mntmn/amiga2000-gfxcard/pics/proto1/oe-patch.jpg

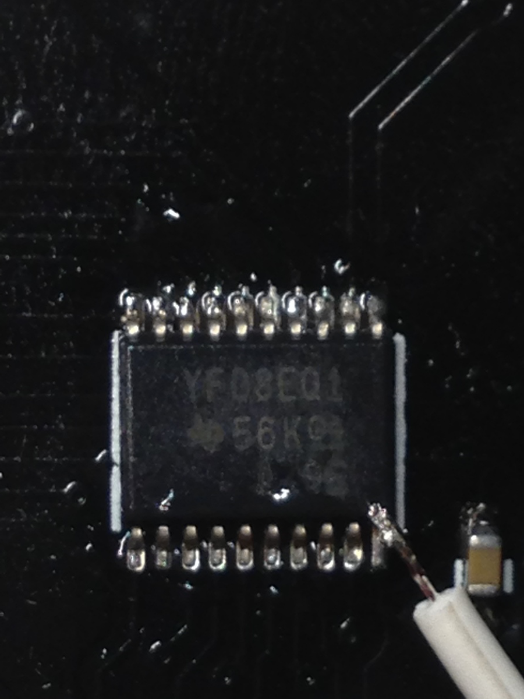
pics/proto1/oe-patch.jpg
