mntmn/amiga2000-gfxcard/pics/proto1/proto1-pcb.png

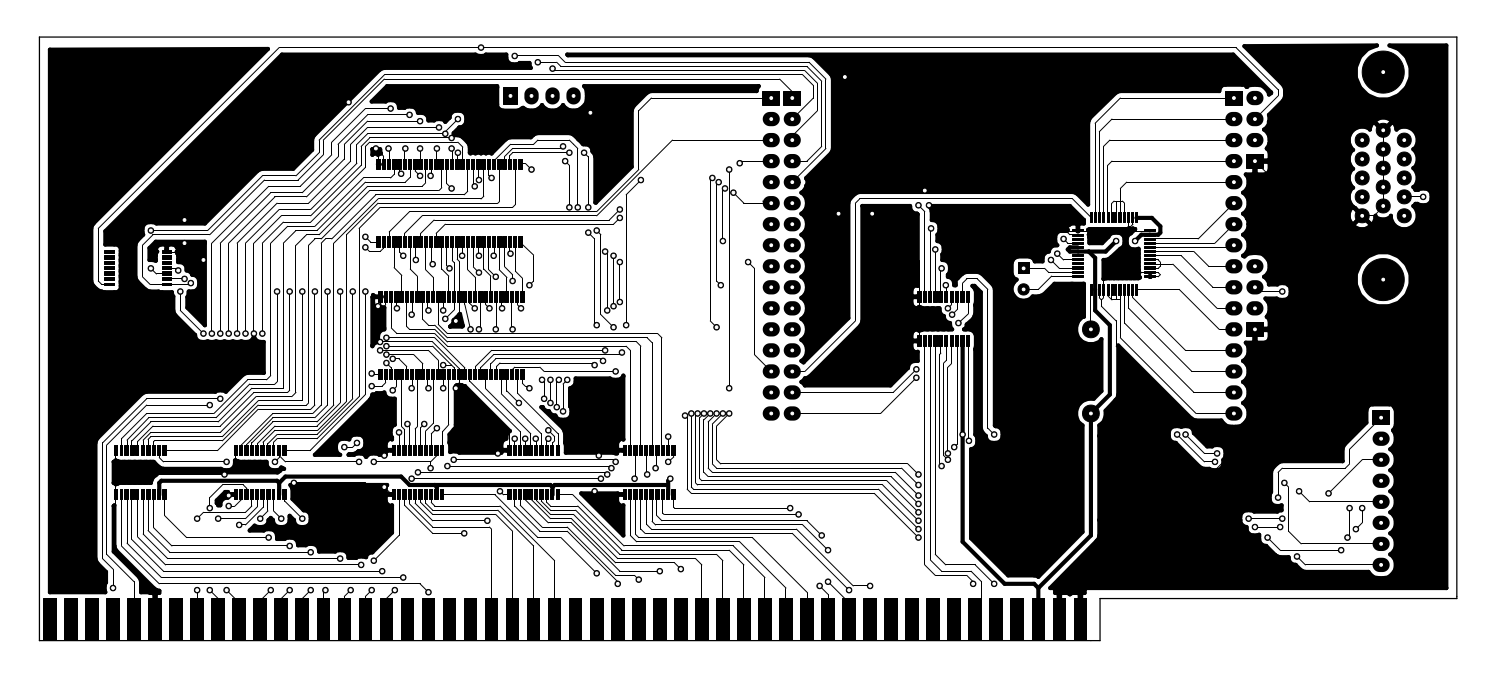
pics/proto1/proto1-pcb.png
