mntmn/amiga2000-gfxcard/pics/proto1/proto1-signals1.jpg

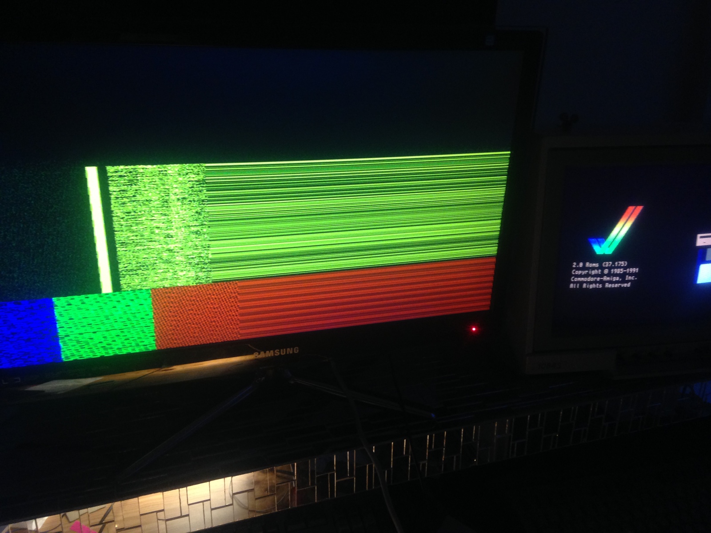
pics/proto1/proto1-signals1.jpg
