mntmn/amiga2000-gfxcard/pics/proto1/zorro-signals1.jpg

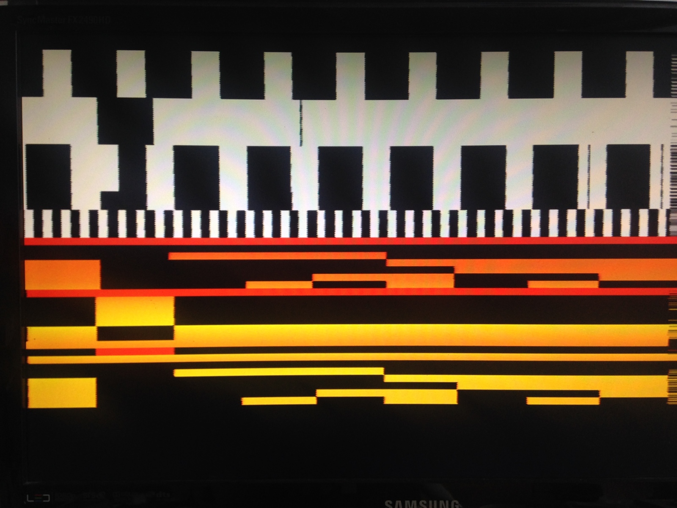
pics/proto1/zorro-signals1.jpg
