mntmn/amiga2000-gfxcard/pics/proto2/proto2-mysticview.jpg

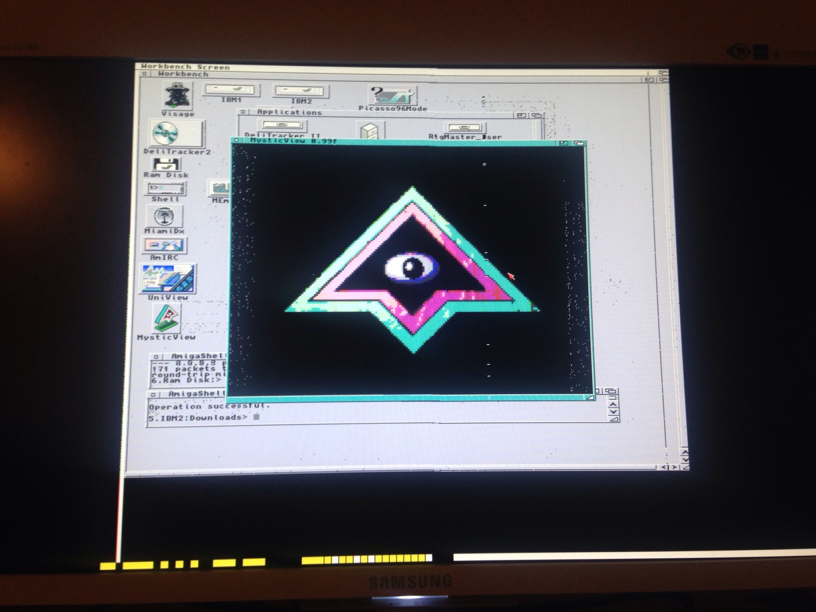
pics/proto2/proto2-mysticview.jpg
