mntmn/amiga2000-gfxcard/pics/proto2/proto2-populated1.jpg

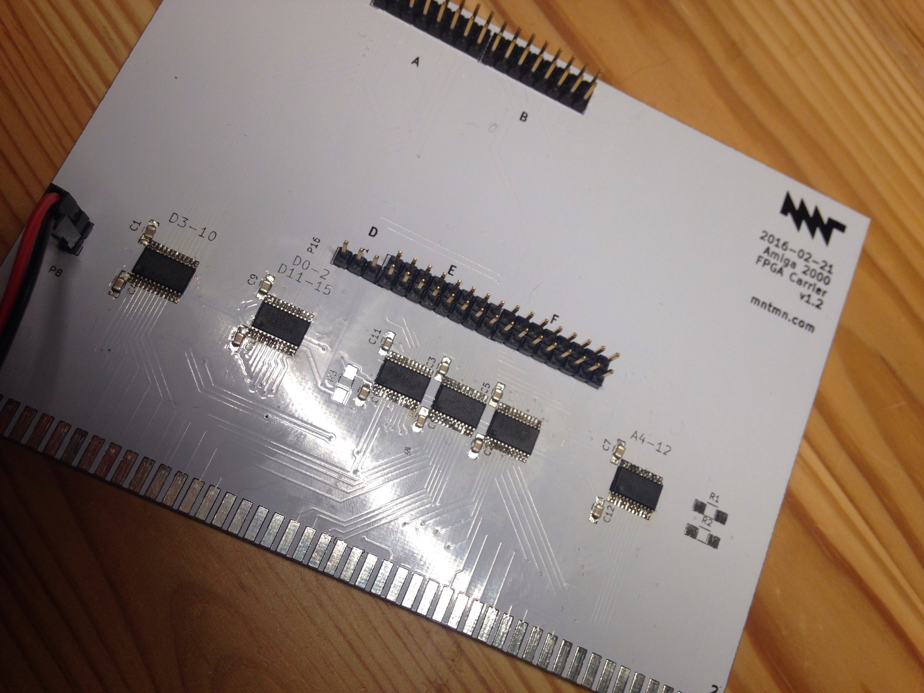
pics/proto2/proto2-populated1.jpg
