mntmn/amiga2000-gfxcard/pics/proto2/proto2-shell.jpg

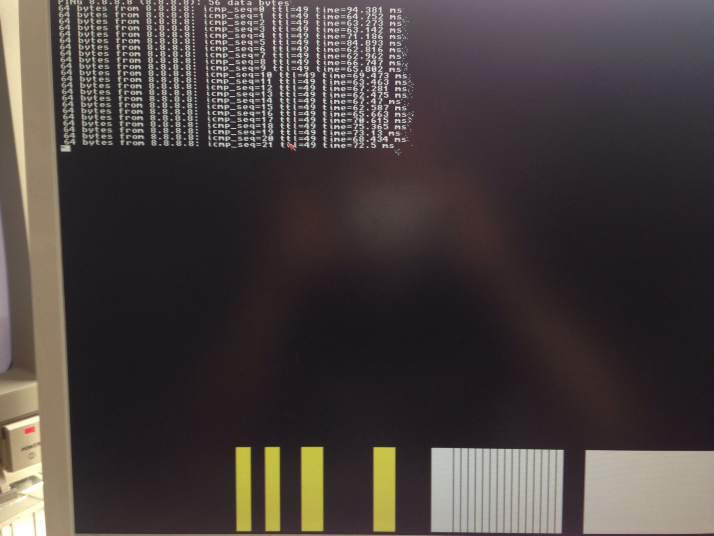
pics/proto2/proto2-shell.jpg
