mntmn/amiga2000-gfxcard/pics/proto2/proto2-signals.jpg

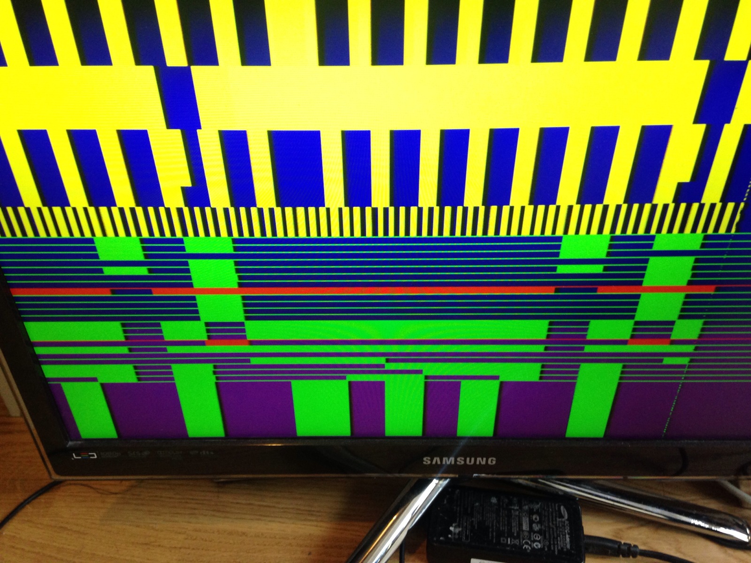
pics/proto2/proto2-signals.jpg
