mntmn/amiga2000-gfxcard/va2000-spartan6/dvid_out.vhd

--------------------------------------------------------------------------------
-- Engineer:      Mike Field <hamster@snap.net.nz>
-- Description:   Converts VGA signals into DVID bitstreams.
--
--                'blank' must be asserted during the non-display 
--                portions of the frame
--
-- NOTE due to the PLL frequency limits, changes are needed in dvid_out_clocking
-- to select pixel rates between 40 and 100 Mhz pixel clocks, or between 20 and 
-- 50 MHz.
--------------------------------------------------------------------------------
library IEEE;
use IEEE.STD_LOGIC_1164.ALL;
Library UNISIM;
use UNISIM.vcomponents.all;

entity dvid_out is
  Port ( -- Clocking
    clk_pixel : IN std_logic;
    -- Pixel data
    red_p     : in  STD_LOGIC_VECTOR (7 downto 0);
    green_p   : in  STD_LOGIC_VECTOR (7 downto 0);
    blue_p    : in  STD_LOGIC_VECTOR (7 downto 0);
    blank     : in  STD_LOGIC;
    hsync     : in  STD_LOGIC;
    vsync     : in  STD_LOGIC;
    reset : in STD_LOGIC;
    -- TMDS outputs
    tmds_out_p : out  STD_LOGIC_VECTOR(3 downto 0);
    tmds_out_n : out  STD_LOGIC_VECTOR(3 downto 0)
  );
end dvid_out;

architecture Behavioral of dvid_out is
  COMPONENT dvid_out_clocking
  PORT(
    clk_pixel : IN std_logic;
    reset : IN std_logic;
    clk_x1 : OUT std_logic;
    clk_x2 : OUT std_logic;
    clk_x10 : OUT std_logic;
    serdes_strobe : OUT std_logic
  );
  END COMPONENT;

  COMPONENT TMDS_encoder
  PORT(
    clk     : IN  std_logic;
    data    : IN  std_logic_vector(7 downto 0);
    c       : IN  std_logic_vector(1 downto 0);
    blank   : IN  std_logic;          
    encoded : OUT std_logic_vector(9 downto 0)
  );
  END COMPONENT;

  COMPONENT tmds_out_fifo
  PORT (
    wr_clk     : IN  STD_LOGIC;
    rd_clk     : IN  STD_LOGIC;
    din        : IN  STD_LOGIC_VECTOR(29 DOWNTO 0);
    wr_en      : IN  STD_LOGIC;
    rd_en      : IN  STD_LOGIC;
    dout       : OUT STD_LOGIC_VECTOR(29 DOWNTO 0);
    full       : OUT STD_LOGIC;
    empty      : OUT STD_LOGIC;
    prog_empty : OUT STD_LOGIC
  );
  END COMPONENT;

  COMPONENT output_serialiser
  PORT(
    clk_load   : IN  std_logic;
    clk_output : IN  std_logic;
    strobe     : IN  std_logic;
    ser_data   : IN  std_logic_vector(4 downto 0);        
    reset   : IN  std_logic;  
    ser_output : OUT std_logic
		);
  END COMPONENT;

  signal clk_x1          : std_logic;
  signal clk_x2          : std_logic;
  signal clk_x10         : std_logic;
  signal serdes_strobe   : std_logic;

  signal encoded_red, encoded_green, encoded_blue : std_logic_vector(9 downto 0);
  signal latched_red, latched_green, latched_blue : std_logic_vector(9 downto 0) := (others => '0');
  signal ser_in_red,  ser_in_green,  ser_in_blue, ser_in_clock   : std_logic_vector(4 downto 0) := (others => '0');
  signal fifo_in       : std_logic_vector(29 downto 0);
  signal fifo_out      : std_logic_vector(29 downto 0);
  signal rd_enable     : std_logic := '0';
  signal not_ready_yet : std_logic;

  signal c_red       : std_logic_vector(1 downto 0); -- := (others => '0');
  signal c_green     : std_logic_vector(1 downto 0); -- := (others => '0');
  signal c_blue      : std_logic_vector(1 downto 0);

  signal red_s     : STD_LOGIC;
  signal green_s   : STD_LOGIC;
  signal blue_s    : STD_LOGIC;
  signal clock_s   : STD_LOGIC;

begin   
  -- Send the pixels to the encoder
  c_blue <= "00"; -- vsync & hsync;
  c_red <= vsync & hsync;
  c_green <= "00"; -- vsync & hsync;
  TMDS_encoder_red:   TMDS_encoder PORT MAP(clk => clk_pixel, data => red_p,   c => c_red,   blank => blank, encoded => encoded_red);
  TMDS_encoder_green: TMDS_encoder PORT MAP(clk => clk_pixel, data => green_p, c => c_green, blank => blank, encoded => encoded_green);
  TMDS_encoder_blue:  TMDS_encoder PORT MAP(clk => clk_pixel, data => blue_p,  c => c_blue,  blank => blank, encoded => encoded_blue);

  -- Then to a small FIFO
  fifo_in <= encoded_red & encoded_green & encoded_blue;

  Inst_dvid_out_clocking: dvid_out_clocking PORT MAP(
    clk_pixel     => clk_pixel,
    clk_x1        => clk_x1,
    clk_x2        => clk_x2,
    clk_x10       => clk_x10,
    serdes_strobe => serdes_strobe,
    reset => reset
  );

  out_fifo: tmds_out_fifo PORT MAP (
    wr_clk => clk_pixel,
    din    => fifo_in,
    wr_en  => '1',
    full   => open,
    
    rd_clk     => clk_x2,
    rd_en      => rd_enable,
    dout       => fifo_out,
    empty      => open,
    prog_empty => not_ready_yet
  );
   
-- Now at a x2 clock, send the data from the fifo to the serialisers
process(clk_x2)
  begin
    if rising_edge(clk_x2) then
      if not_ready_yet = '0' then
        if rd_enable = '1' then
          ser_in_red   <= fifo_out(29 downto 25);
          ser_in_green <= fifo_out(19 downto 15);
          ser_in_blue  <= fifo_out( 9 downto  5);
          ser_in_clock <= "11111";
          rd_enable <= '0';
        else
          ser_in_red   <= fifo_out(24 downto 20);
          ser_in_green <= fifo_out(14 downto 10);
          ser_in_blue  <= fifo_out( 4 downto  0);
          ser_in_clock <= "00000";
          rd_enable <= '1';
        end if;
      end if;
    end if;
  end process; 

  -- The Serialisers
  output_serialiser_r: output_serialiser PORT MAP(clk_load => clk_x2, clk_output => clk_x10, strobe => serdes_strobe, ser_data => ser_in_red,   ser_output => red_s, reset => reset);
  output_serialiser_g: output_serialiser PORT MAP(clk_load => clk_x2, clk_output => clk_x10, strobe => serdes_strobe, ser_data => ser_in_green, ser_output => green_s, reset => reset);
  output_serialiser_b: output_serialiser PORT MAP(clk_load => clk_x2, clk_output => clk_x10, strobe => serdes_strobe, ser_data => ser_in_blue,  ser_output => blue_s, reset => reset);
  output_serialiser_c: output_serialiser PORT MAP(clk_load => clk_x2, clk_output => clk_x10, strobe => serdes_strobe, ser_data => ser_in_clock, ser_output => clock_s, reset => reset);

  -- The output buffers/drivers
  OBUFDS_red   : OBUFDS port map ( O  => tmds_out_p(0), OB => tmds_out_n(0), I => red_s);
  OBUFDS_green : OBUFDS port map ( O  => tmds_out_p(1), OB => tmds_out_n(1), I => green_s);
  OBUFDS_blue  : OBUFDS port map ( O  => tmds_out_p(2), OB => tmds_out_n(2), I => blue_s);
  OBUFDS_clock : OBUFDS port map ( O  => tmds_out_p(3), OB => tmds_out_n(3), I => clock_s);

end Behavioral;
